manji-0/nfc-business-card/assets/nfc-n-mark-preview.png

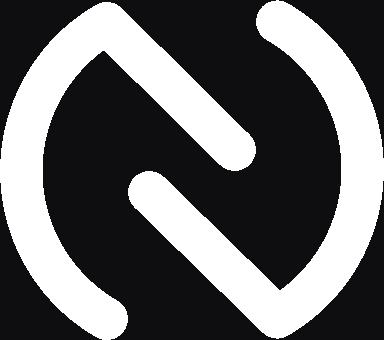
assets/nfc-n-mark-preview.png
