manji-0/nfc-business-card/assets/profile-mono-preview.png

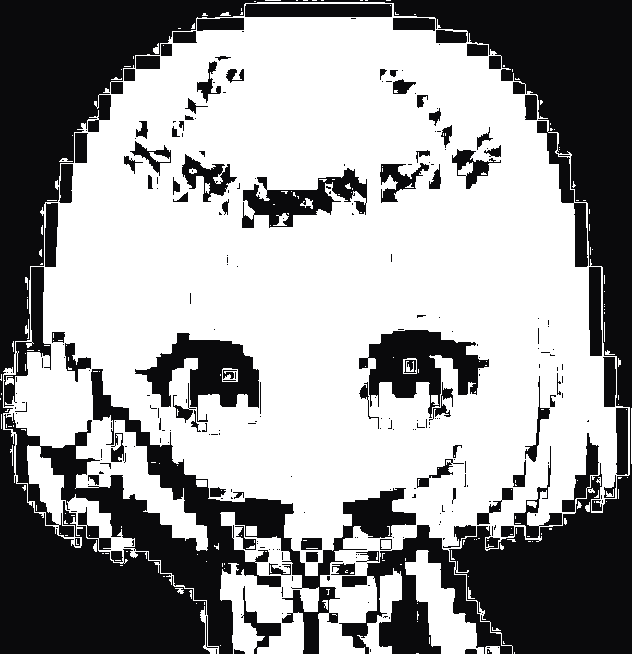
assets/profile-mono-preview.png
