manji-0/nfc-business-card/fab/preview.png

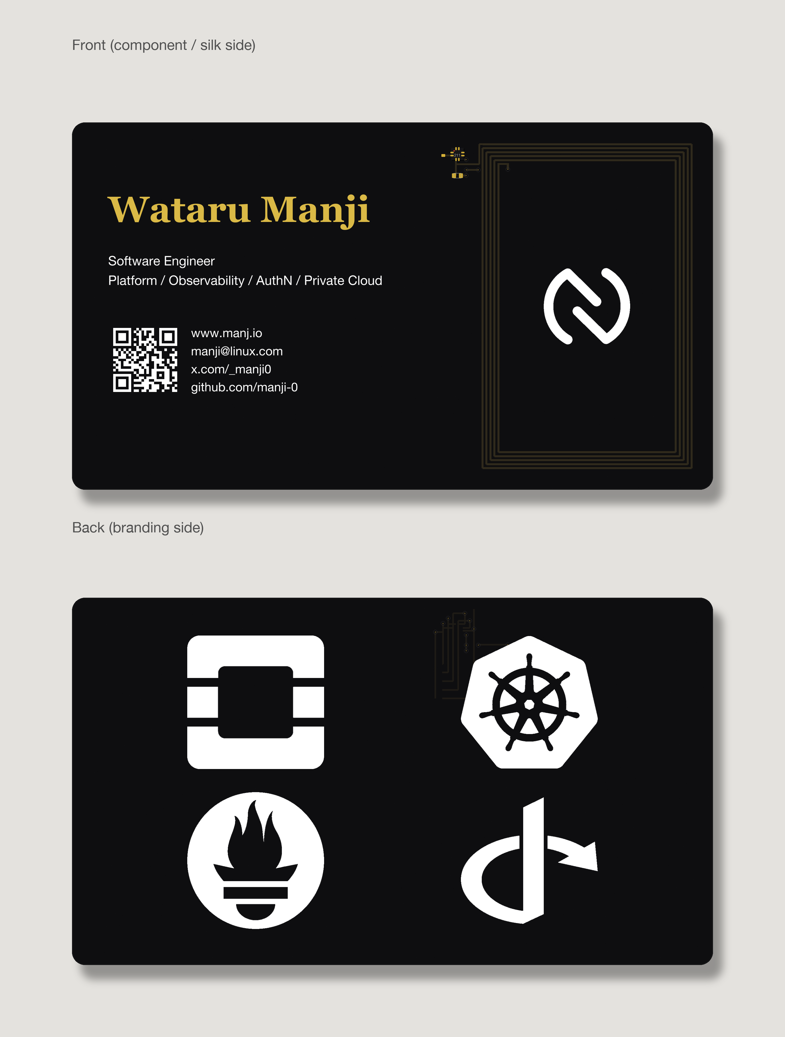
fab/preview.png
